yuburoll/ilwol/images/ilwolPhotoHeader.jpg

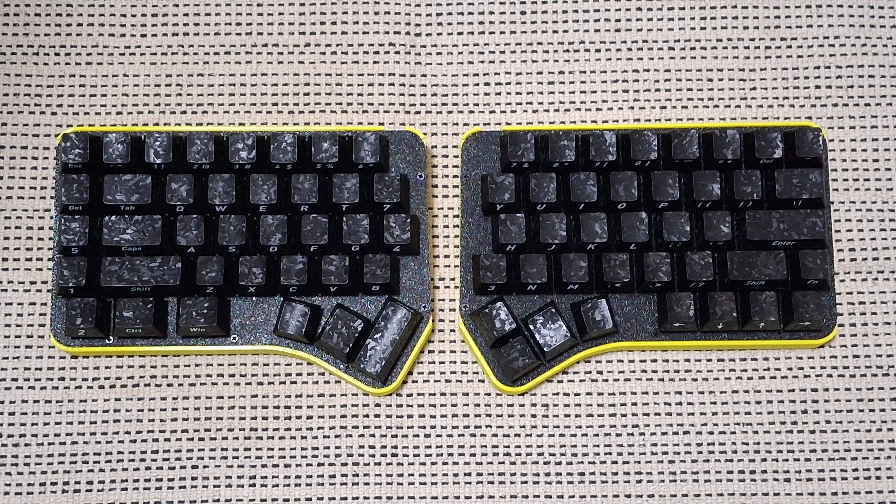
images/ilwolPhotoHeader.jpg
