yuburoll/ilwol/case/step/ilwolCaseBuffedL.stp

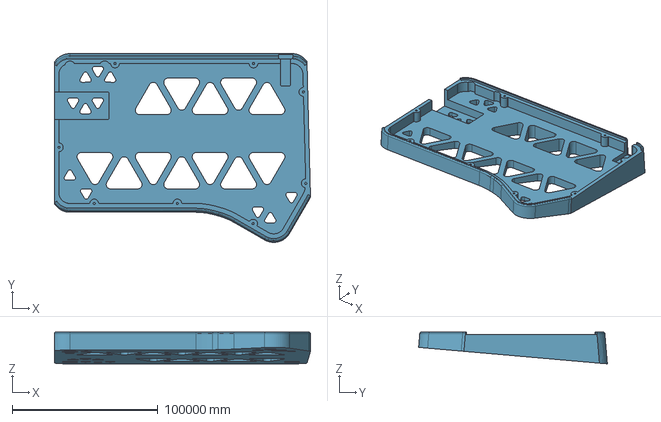
[picture p23: CAD file, 2026-06-19]
case/step/ilwolCaseBuffedL.stp
175600.3 x 129534.7 x 21788.4 mm
