yuburoll/ilwol/case/step/ilwolCaseR.stp

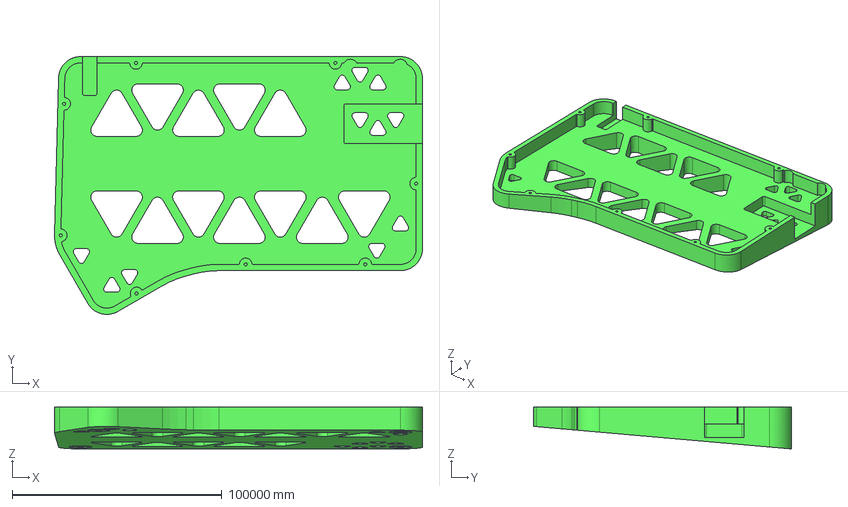
[picture p24: CAD file, 2026-06-18]
case/step/ilwolCaseR.stp
175344.4 x 122841.3 x 19954.9 mm
