yuburoll/ilwol/case/step/ilwolCaseRoundBuffedR.stp

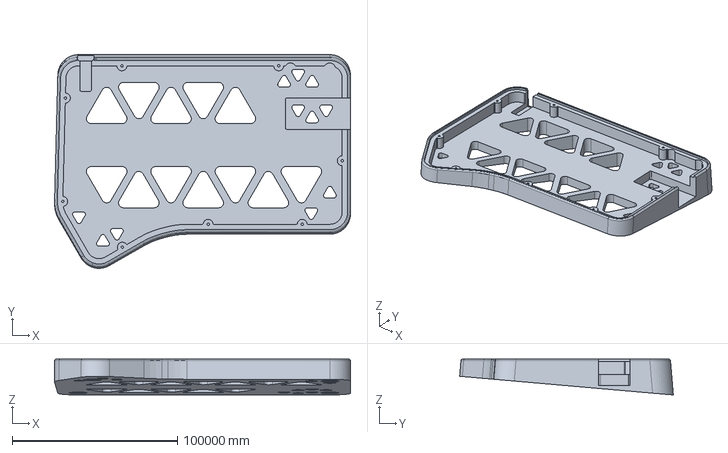
[picture p25: CAD file, 2026-06-18]
case/step/ilwolCaseRoundBuffedR.stp
179373.6 x 129534.5 x 21788.4 mm
