yuburoll/ilwol/kicad/ilwol.kicad_sch

## KiCad design kicad/ilwol.kicad_sch (2026-05-22)

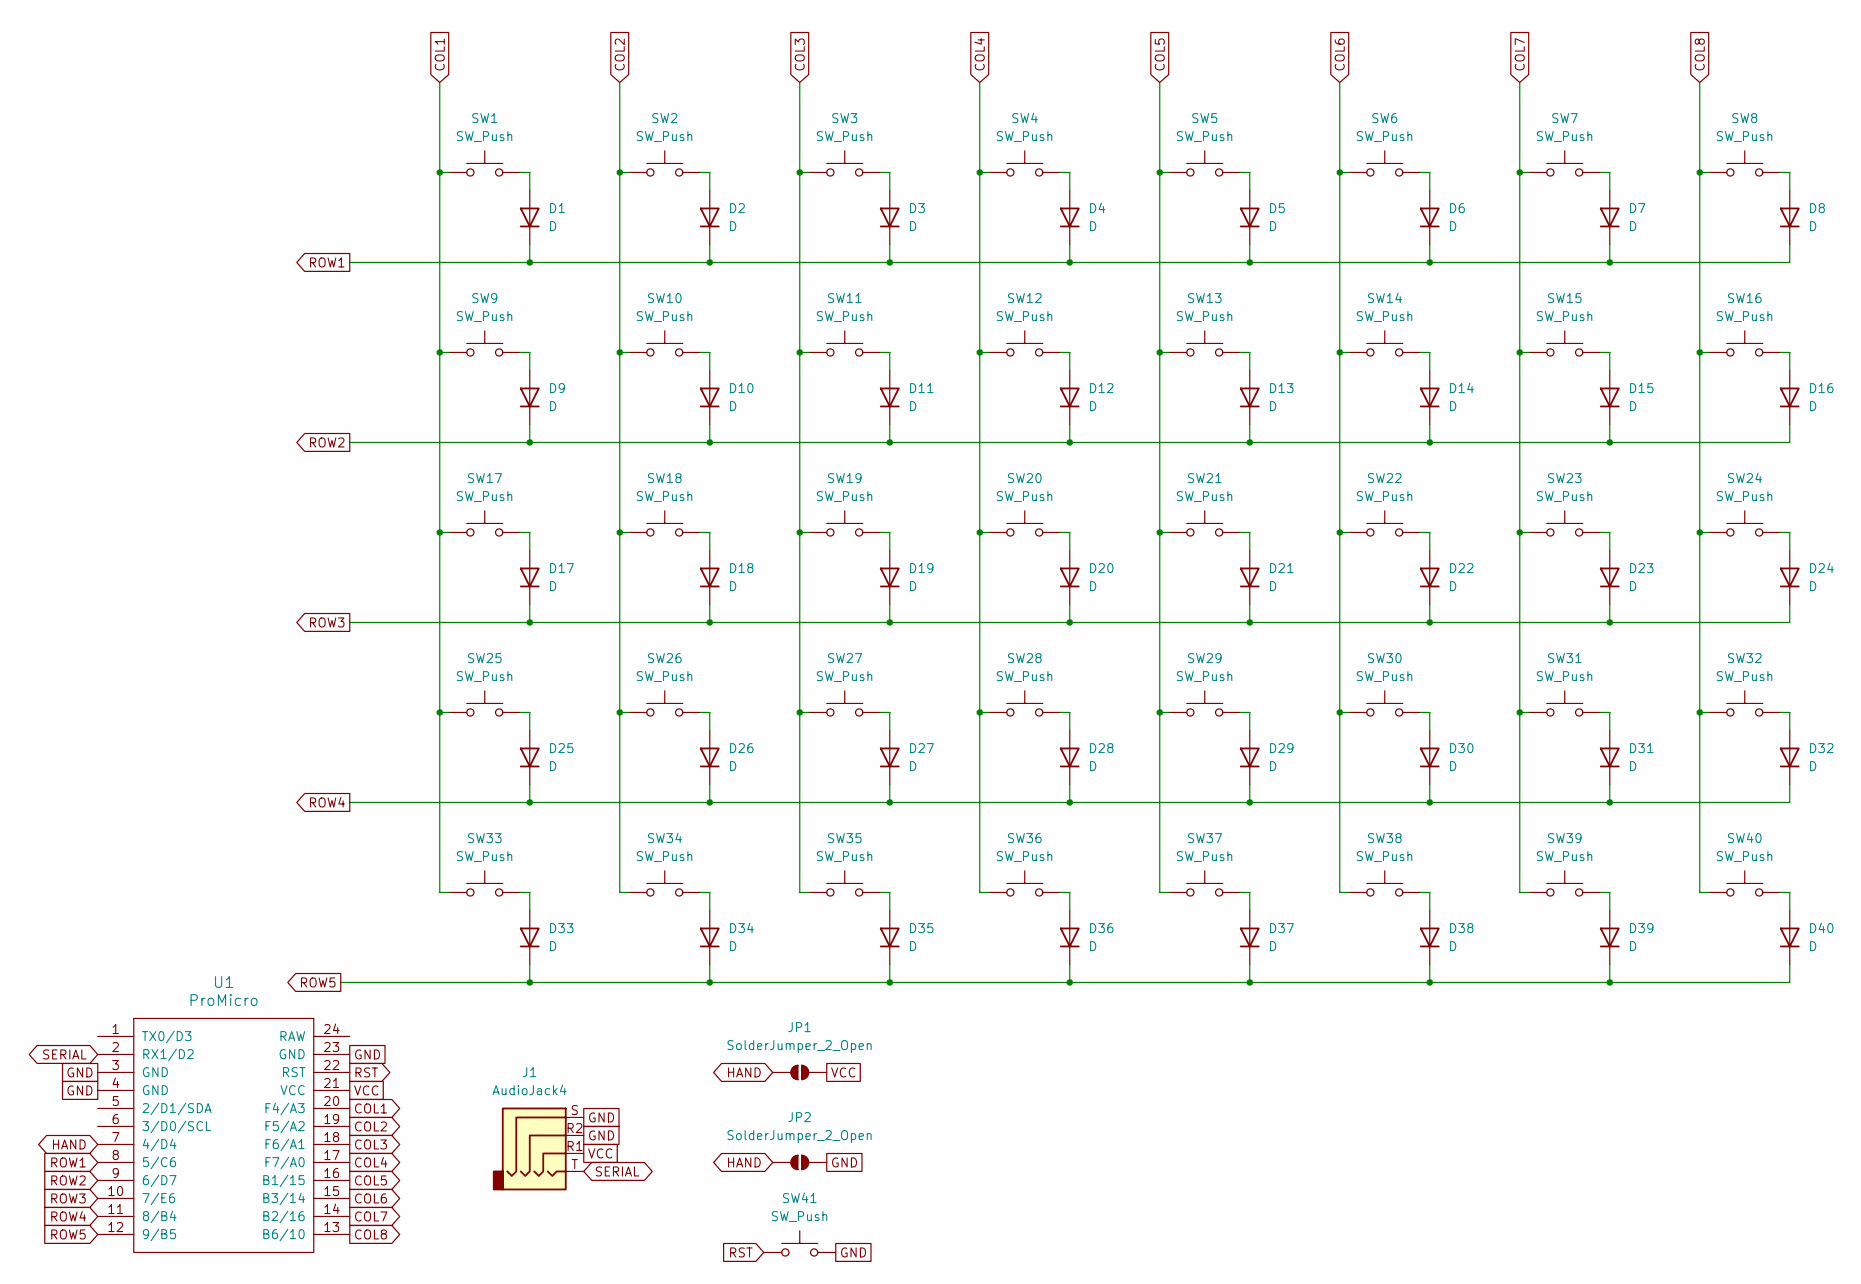
[picture p49: schematic ilwol.kicad_sch]

Parts:
D1, D2, D3, D4, D5, D6, D7, D8, D9, D10, D11, D12, D13, D14, D15, D16, D17, D18, D19, D20, D21, D22, D23, D24, D25, D26, D27, D28, D29, D30, D31, D32, D33, D34, D35, D36, D37, D38, D39, D40: D
J1: AudioJack4
JP1, JP2: SolderJumper_2_Open
SW1, SW2, SW3, SW4, SW5, SW6, SW7, SW8, SW9, SW10, SW11, SW12, SW13, SW14, SW15, SW16, SW17, SW18, SW19, SW20, SW21, SW22, SW23, SW24, SW25, SW26, SW27, SW28, SW29, SW30, SW31, SW32, SW33, SW34, SW35, SW36, SW37, SW38, SW39, SW40, SW41: SW_Push
U1: ProMicro

Connections:
COL1: SW1.1, SW9.1, SW17.1, SW25.1, SW33.1, U1.20 (F4/A3)
COL2: SW2.1, SW10.1, SW18.1, SW26.1, SW34.1, U1.19 (F5/A2)
COL3: SW3.1, SW11.1, SW19.1, SW27.1, SW35.1, U1.18 (F6/A1)
COL4: SW4.1, SW12.1, SW20.1, SW28.1, SW36.1, U1.17 (F7/A0)
COL5: SW5.1, SW13.1, SW21.1, SW29.1, SW37.1, U1.16 (B1/15)
COL6: SW6.1, SW14.1, SW22.1, SW30.1, SW38.1, U1.15 (B3/14)
COL7: SW7.1, SW15.1, SW23.1, SW31.1, SW39.1, U1.14 (B2/16)
COL8: SW8.1, SW16.1, SW24.1, SW32.1, SW40.1, U1.13 (B6/10)
GND: J1.R2, J1.S, JP2.2 (B), SW41.2, U1.3 (GND), U1.4 (GND), U1.23 (GND)
HAND: JP1.1 (A), JP2.1 (A), U1.7 (4/D4)
unnamed: D1.2 (A), SW1.2
unnamed: D2.2 (A), SW2.2
unnamed: D3.2 (A), SW3.2
unnamed: D4.2 (A), SW4.2
unnamed: D5.2 (A), SW5.2
unnamed: D6.2 (A), SW6.2
unnamed: D7.2 (A), SW7.2
unnamed: D8.2 (A), SW8.2
unnamed: D9.2 (A), SW9.2
unnamed: D10.2 (A), SW10.2
unnamed: D11.2 (A), SW11.2
unnamed: D12.2 (A), SW12.2
unnamed: D13.2 (A), SW13.2
unnamed: D14.2 (A), SW14.2
unnamed: D15.2 (A), SW15.2
unnamed: D16.2 (A), SW16.2
unnamed: D17.2 (A), SW17.2
unnamed: D18.2 (A), SW18.2
unnamed: D19.2 (A), SW19.2
unnamed: D20.2 (A), SW20.2
unnamed: D21.2 (A), SW21.2
unnamed: D22.2 (A), SW22.2
unnamed: D23.2 (A), SW23.2
unnamed: D24.2 (A), SW24.2
unnamed: D25.2 (A), SW25.2
unnamed: D26.2 (A), SW26.2
unnamed: D27.2 (A), SW27.2
unnamed: D28.2 (A), SW28.2
unnamed: D29.2 (A), SW29.2
unnamed: D30.2 (A), SW30.2
unnamed: D31.2 (A), SW31.2
unnamed: D32.2 (A), SW32.2
unnamed: D33.2 (A), SW33.2
unnamed: D34.2 (A), SW34.2
unnamed: D35.2 (A), SW35.2
unnamed: D36.2 (A), SW36.2
unnamed: D37.2 (A), SW37.2
unnamed: D38.2 (A), SW38.2
unnamed: D39.2 (A), SW39.2
unnamed: D40.2 (A), SW40.2
ROW1: D1.1 (K), D2.1 (K), D3.1 (K), D4.1 (K), D5.1 (K), D6.1 (K), D7.1 (K), D8.1 (K), U1.8 (5/C6)
ROW2: D9.1 (K), D10.1 (K), D11.1 (K), D12.1 (K), D13.1 (K), D14.1 (K), D15.1 (K), D16.1 (K), U1.9 (6/D7)
ROW3: D17.1 (K), D18.1 (K), D19.1 (K), D20.1 (K), D21.1 (K), D22.1 (K), D23.1 (K), D24.1 (K), U1.10 (7/E6)
ROW4: D25.1 (K), D26.1 (K), D27.1 (K), D28.1 (K), D29.1 (K), D30.1 (K), D31.1 (K), D32.1 (K), U1.11 (8/B4)
ROW5: D33.1 (K), D34.1 (K), D35.1 (K), D36.1 (K), D37.1 (K), D38.1 (K), D39.1 (K), D40.1 (K), U1.12 (9/B5)
RST: SW41.1, U1.22 (RST)
SERIAL: J1.T, U1.2 (RX1/D2)
VCC: J1.R1, JP1.2 (B), U1.21 (VCC)
